SponringDominik/Slope-Sensor/src/SlopeSensor/lcd_util.h

/************************************************************************/
/* Hilfs-Funktionen für den LCD-Driver BU91796                          */
/************************************************************************/
#ifndef LCD_UTIL_H_
#define LCD_UTIL_H_



/* Initierungsvorgang des LCD-Displays */
void lcd_init(void);

/* Beschreiben des LCD-Speichers */
void lcd_write(int8_t);



#endif /* LCD_UTIL_H_ */
